SamLeft222/openflight/src/openflight/iwr6843/monitor.py

"""IWR6843 L3 capture, triggered by a GPIO edge or by the radar itself.

With ``auto_trigger`` the firmware detects the shot (autotrigger.py) and sends
a notice instead of the sound sensor's GPIO edge; each notice becomes the same
trigger edge, so everything downstream is unchanged.
"""

from __future__ import annotations

import logging
import queue
import threading
import time
from collections import deque
from dataclasses import dataclass
from datetime import datetime
from pathlib import Path
from typing import Callable

from openflight.gpio_factory import ensure_lgpio_pin_factory
from openflight.iwr6843.autotrigger import AutoTriggerConfig
from openflight.iwr6843.driver import IWR6843Radar
from openflight.iwr6843.dump import HEADER, parse_header, payload_nbytes
from openflight.iwr6843.reduced import StripRequest, parse_overview

logger = logging.getLogger(__name__)

_GRACEFUL_DUMP_SHUTDOWN_S = 12.0
# A held reduced-transfer capture nobody finishes is released after this long:
# under the firmware's own 10 s timeout, so the Pi's state never disagrees.
DEFAULT_HOLD_BUDGET_S = 8.0
# How long one notice poll holds the serial port between captures.
_NOTICE_POLL_S = 0.05


def frame_period_s_from_config(config_path: str | Path) -> float:
    """The frame period from a cfg's ``frameCfg`` (its fifth field, in ms)."""
    with Path(config_path).open(encoding="utf-8") as handle:
        for raw_line in handle:
            fields = raw_line.split()
            if fields and fields[0] == "frameCfg" and len(fields) >= 6:
                return float(fields[5]) / 1000.0
    raise ValueError(f"IWR6843 config {config_path} has no frameCfg")


def tx_order_from_config(config_path: str | Path) -> str:
    """Infer the vertical physical TX order from chirp masks in a cfg."""
    masks = []
    with Path(config_path).open(encoding="utf-8") as handle:
        for raw_line in handle:
            line = raw_line.strip()
            if line.startswith("chirpCfg"):
                masks.append(line.rsplit(maxsplit=1)[-1])
    if masks == ["1", "4"]:
        return "normal"
    if masks == ["4", "1"]:
        return "reversed"
    if masks == ["1", "2", "4"]:
        return "normal"
    raise ValueError(f"IWR6843 config must contain chirp TX masks 1/4, 4/1, or 1/2/4, got {masks}")


@dataclass(frozen=True)
class IWR6843Capture:
    """One GPIO edge and its completed L3 dump, or its reduced-transfer overview.

    ``transfer`` is "full" (``raw`` holds the dump) or "reduced" (``overview``
    holds the overview, and the radar holds the frozen ring until
    ``IWR6843CaptureMonitor.finish_capture``). ``fallback_reason`` says why a
    reduced-mode monitor fell back to a full dump.
    """

    sequence: int
    trigger_timestamp: float
    completed_timestamp: float
    dump_duration_s: float
    raw: bytes | None
    path: Path | None
    error: str | None = None
    temperature_report: dict[str, int] | None = None
    overview: bytes | None = None
    transfer: str = "full"
    fallback_reason: str | None = None

    @property
    def valid(self) -> bool:
        """Whether a complete dump or overview was captured."""
        return (self.raw is not None or self.overview is not None) and self.error is None


@dataclass
class _Hold:
    """The capture whose frozen ring the radar is holding.

    ``done`` wakes the capture thread: set when the hold is finished, or when
    the OPS rejects the sound (``rejected``) so the thread releases it now.
    A capture ``claimed`` by a shot is never released by a rejection.
    """

    sequence: int
    edge_timestamp: float
    done: threading.Event
    finished: bool = False
    rejected: bool = False
    claimed: bool = False


class IWR6843CaptureMonitor:
    """Capture TI rolling-buffer dumps on the same sound edge used by OPS.

    The GPIO callback only timestamps and queues the edge. Serial transfer is
    handled on a dedicated thread because one 768 KiB dump takes several
    seconds at the firmware UART rate.
    """

    def __init__(
        self,
        *,
        config_path: str | Path,
        output_dir: str | Path,
        port: str | None = None,
        gpio_pin: int = 17,
        radar: IWR6843Radar | None = None,
        button_factory: Callable | None = None,
        match_tolerance_s: float = 0.75,
        save_dumps: bool = False,
        trigger_observers: list[Callable[[float], None]] | None = None,
        reduced_gate: tuple[int, int] | None = None,
        hold_budget_s: float = DEFAULT_HOLD_BUDGET_S,
        auto_trigger: AutoTriggerConfig | None = None,
    ):
        self.config_path = Path(config_path)
        self.output_dir = Path(output_dir).expanduser()
        self.gpio_pin = gpio_pin
        self.match_tolerance_s = match_tolerance_s
        self.save_dumps = save_dumps
        self.radar = radar or IWR6843Radar(port=port)
        self._button_factory = button_factory
        self._button = None
        self._running = False
        self._armed = False
        self._capture_active = False
        self._sequence = 0
        self._last_edge_timestamp = 0.0
        self._events: queue.Queue[float | None] = queue.Queue(maxsize=1)
        self._captures: deque[IWR6843Capture] = deque()
        self._condition = threading.Condition()
        self._worker: threading.Thread | None = None
        self._trigger_observers = list(trigger_observers or [])
        # Reduced transfer (plans/iwr6843-on-chip-reduction.md): None keeps the
        # classic full dump. All radar I/O while a ring is held goes through
        # _serial_lock; _hold names the held capture.
        self.reduced_gate = reduced_gate
        self.hold_budget_s = hold_budget_s
        # Re-entrant: the full-dump fallback reads the ring inside a locked call.
        self._serial_lock = threading.RLock()
        self._hold: _Hold | None = None
        # The radar's own shot detector instead of the GPIO edge (needs the
        # reduced transfer, which holds the detected ring).
        self.auto_trigger = auto_trigger
        self._listener: threading.Thread | None = None
        # Edges the OPS rejected before their capture completed.
        self._rejected_edges: deque[float] = deque(maxlen=16)

    @property
    def port(self) -> str:
        """Connected TI serial port."""
        return self.radar.port

    def start(self, *, armed: bool = True) -> None:
        """Configure the radar and GPIO, optionally arming trigger capture."""
        if self._running:
            return
        if not self.config_path.is_file():
            raise FileNotFoundError(f"IWR6843 config not found: {self.config_path}")
        if self.save_dumps:
            self.output_dir.mkdir(parents=True, exist_ok=True)
        configured = False
        try:
            self.radar.send_config(str(self.config_path))
            configured = True
            if self.reduced_gate is not None:
                try:
                    self.radar.configure_overview_gate(self.reduced_gate)
                except RuntimeError as exc:
                    # Released firmware has no overviewCfg: keep the radar
                    # working with full dumps rather than failing the IWR.
                    logger.warning(
                        "[IWR6843] Firmware lacks the reduced transfer (%s); using full dumps",
                        exc,
                    )
                    self.reduced_gate = None
            self._configure_auto_trigger()

            if self.auto_trigger is None:
                button_factory = self._button_factory
                if button_factory is None:
                    # Must precede the first gpiozero device: on a Pi 5 gpiozero's
                    # own auto-detection fails outright. See gpio_factory.
                    ensure_lgpio_pin_factory()

                    from gpiozero import (  # pylint: disable=import-error,import-outside-toplevel
                        Button,
                    )

                    button_factory = Button
                # No gpiozero debounce: lgpio delays delivery by the debounce
                # interval, which previously cost the first 50 ms of ball flight.
                self._button = button_factory(self.gpio_pin, pull_up=False, bounce_time=None)
            self._running = True
            self._worker = threading.Thread(
                target=self._capture_loop,
                name="iwr6843-capture",
                daemon=True,
            )
            self._worker.start()
            if self.auto_trigger is not None:
                self._listener = threading.Thread(
                    target=self._notice_loop,
                    name="iwr6843-auto-trigger",
                    daemon=True,
                )
                self._listener.start()
            if armed:
                self.arm()
        except Exception:
            self._running = False
            if self._button is not None:
                self._button.close()
                self._button = None
            if configured:
                self._stop_sensor_and_close()
            else:
                self.radar.close()
            raise
        logger.info(
            "[IWR6843] Configured on %s using %s (%s%s)",
            "its own shot detector" if self.auto_trigger else f"BCM{self.gpio_pin}",
            self.port,
            self.config_path.name,
            ", armed" if self._armed else ", waiting for OPS",
        )

    def _configure_auto_trigger(self) -> None:
        """Enable the firmware's detector, or fall back to the GPIO edge."""
        if self.auto_trigger is None:
            return
        if self.reduced_gate is None:
            logger.warning("[IWR6843] Auto trigger needs the reduced transfer; using the GPIO edge")
            self.auto_trigger = None
            return
        try:
            self.radar.configure_auto_trigger(self.auto_trigger)
        except RuntimeError as exc:
            logger.warning(
                "[IWR6843] Firmware lacks the shot detector (%s); using the GPIO edge", exc
            )
            self.auto_trigger = None
            return
        self._frame_period_s = frame_period_s_from_config(self.config_path)
        logger.info("[IWR6843] Shot detector on: %s", self.auto_trigger.command())

    def _notice_loop(self) -> None:
        """Turn the radar's shot notices into trigger edges between captures."""
        while self._running:
            with self._condition:
                idle = not self._capture_active and self._events.empty()
            if not idle:
                time.sleep(0.01)
                continue
            try:
                with self._serial_lock:
                    notice = self.radar.read_auto_trigger_notice(timeout_s=_NOTICE_POLL_S)
            except Exception:  # pylint: disable=broad-exception-caught
                logger.warning("[IWR6843] Shot notice read failed", exc_info=True)
                time.sleep(0.1)
                continue
            if notice is None:
                continue
            edge = notice.detection_timestamp(self._frame_period_s)
            logger.info(
                "[IWR6843] Radar detected a shot (#%d, club at bin %d, %.1f bins/frame)",
                notice.seq,
                notice.end_bin,
                notice.slope_q / 4.0,
            )
            if not self.notify_trigger(edge):
                # Not armed yet (or already busy): the radar is holding a ring
                # nobody will fetch. Let it go rather than wait for a timeout.
                logger.info("[IWR6843] Shot notice ignored; releasing the radar")
                try:
                    with self._serial_lock:
                        self.radar.release()
                except Exception:  # pylint: disable=broad-exception-caught
                    logger.warning("[IWR6843] Release after ignored notice failed", exc_info=True)

    def arm(self) -> None:
        """Accept GPIO edges after the OPS trigger path is fully initialized."""
        if not self._running:
            raise RuntimeError("cannot arm an IWR6843 monitor that is not running")
        if self._armed:
            return
        if self._button is not None:
            # Attach while logically disarmed so a line already high from OPS
            # startup cannot synchronously create a false capture.
            self._button.when_pressed = self.notify_trigger
        self._armed = True
        logger.info(
            "[IWR6843] Armed on %s",
            "its own shot detector" if self.auto_trigger else f"BCM{self.gpio_pin}",
        )

    def notify_trigger(self, timestamp: float | None = None) -> bool:
        """Queue a GPIO edge without doing serial work in the callback."""
        if not self._running or not self._armed:
            return False
        edge_timestamp = time.time() if timestamp is None else float(timestamp)
        with self._condition:
            # Reject acoustic ringing and any second edge while the seven-second
            # UART dump is in flight. The OPS side makes the same shot wait.
            if (
                self._capture_active
                or not self._events.empty()
                or edge_timestamp - self._last_edge_timestamp < 0.1
            ):
                logger.debug("[IWR6843] Ignoring duplicate/busy trigger edge")
                return False
            self._last_edge_timestamp = edge_timestamp
            self._events.put_nowait(edge_timestamp)
            self._condition.notify_all()
        for observer in self._trigger_observers:
            try:
                observer(edge_timestamp)
            except Exception:  # pylint: disable=broad-exception-caught
                logger.warning("[IWR6843] Trigger observer failed", exc_info=True)
        return True

    def _validate_dump(self, raw: bytes) -> dict:
        if len(raw) < HEADER.size:
            raise ValueError(f"short IWR6843 dump: {len(raw)} bytes")
        metadata = parse_header(raw)
        expected = metadata["header_nbytes"] + payload_nbytes(metadata, raw)
        if len(raw) != expected:
            raise ValueError(f"short IWR6843 dump: {len(raw)} bytes, expected {expected}")
        return metadata

    def _capture_path(
        self, sequence: int, trigger_timestamp: float, suffix: str = ".l3dump"
    ) -> Path:
        timestamp = datetime.fromtimestamp(trigger_timestamp).strftime("%Y%m%d_%H%M%S_%f")[:-3]
        return self.output_dir / f"iwr6843_{timestamp}_{sequence:03d}{suffix}"

    def _read_full(self, sequence: int, edge_timestamp: float) -> tuple[bytes, Path | None, dict]:
        """One ordinary dump (or the held ring streamed whole), validated and saved."""
        raw = self.radar.read_dump()
        metadata = self._validate_dump(raw)
        path = None
        if self.save_dumps:
            path = self._capture_path(sequence, edge_timestamp)
            path.write_bytes(raw)
        return raw, path, metadata

    def _read_reduced(self, sequence: int, edge_timestamp: float) -> dict:
        """The overview, holding the ring -- or an ordinary dump if that fails."""
        try:
            overview = self.radar.read_overview()
            metadata = parse_overview(overview).metadata
        except Exception as exc:  # pylint: disable=broad-exception-caught
            logger.warning(
                "[IWR6843] Overview #%d failed (%s); falling back to a full dump",
                sequence,
                exc,
            )
            try:
                self.radar.release()
            except Exception:  # pylint: disable=broad-exception-caught
                logger.warning("[IWR6843] Release before fallback failed", exc_info=True)
            raw, path, metadata = self._read_full(sequence, edge_timestamp)
            return {"raw": raw, "path": path, "metadata": metadata, "fallback_reason": str(exc)}
        path = None
        if self.save_dumps:
            path = self._capture_path(sequence, edge_timestamp, ".overview")
            path.write_bytes(overview)
        with self._serial_lock:
            self._hold = _Hold(
                sequence=sequence, edge_timestamp=edge_timestamp, done=threading.Event()
            )
        return {"overview": overview, "path": path, "metadata": metadata, "transfer": "reduced"}

    def read_strips(self, capture: IWR6843Capture, request: StripRequest) -> bytes:
        """Strips of a held capture's frozen ring."""
        with self._serial_lock:
            if not self._holding(capture):
                raise RuntimeError(f"IWR6843 capture #{capture.sequence} is no longer held")
            return self.radar.read_strips(request)

    def finish_capture(self, capture: IWR6843Capture, *, full_dump: bool) -> bytes | None:
        """Let a reduced-transfer capture go; returns the full dump when asked for.
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
